blinkenjim/m404/eagle/m404.sch

## EAGLE design eagle/m404.sch (2017-06-18)

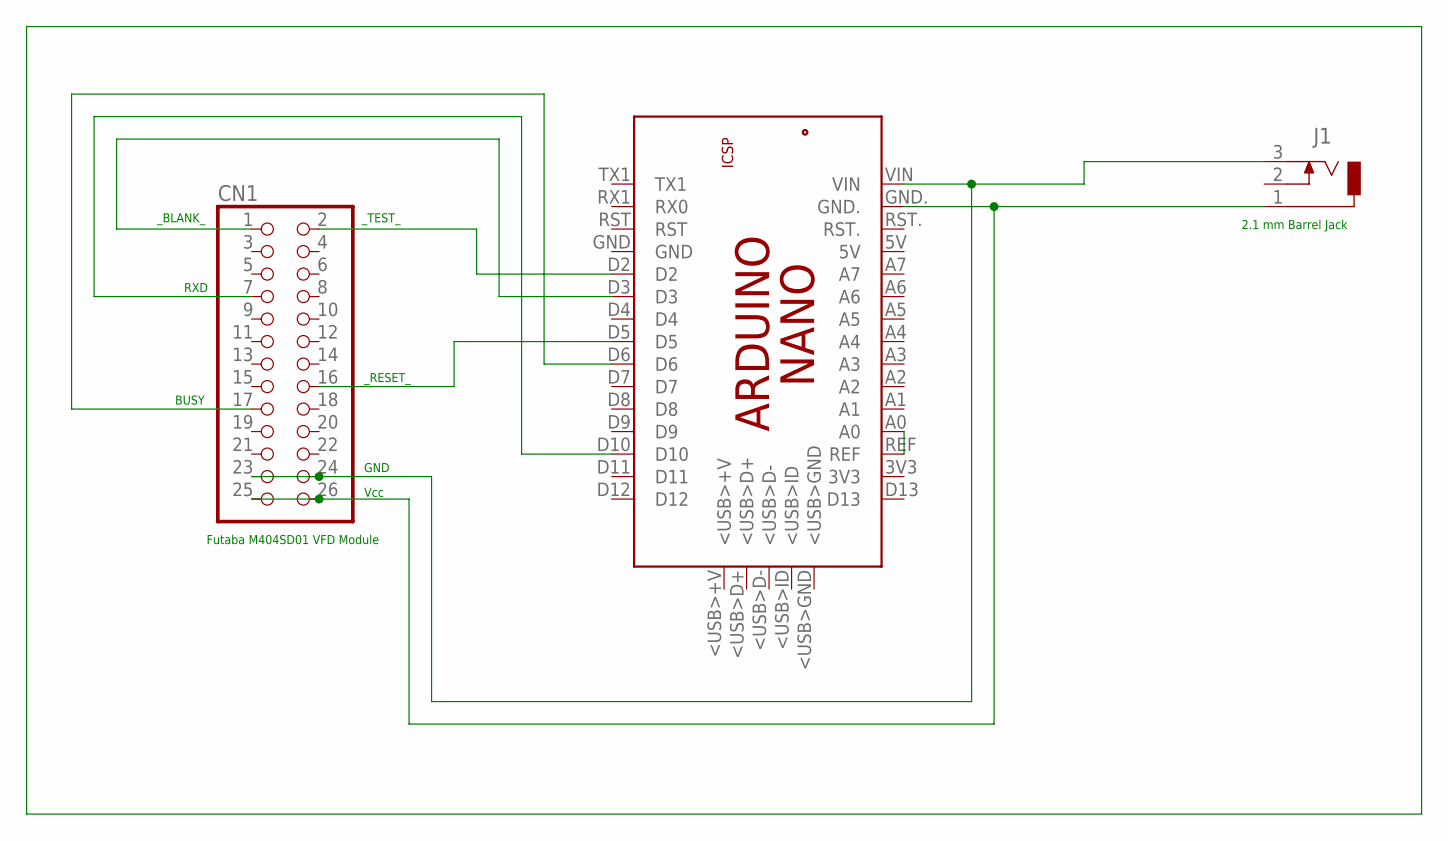
[picture p12: schematic m404.sch]

Parts:
CN1: PINHD-2X13; 2X13
J1: DCJ0202
PCB1: ARDUINO_NANO

Connections:
unnamed: CN1.25, CN1.26, J1.1, PCB1.GND.
unnamed: CN1.1, PCB1.D3
unnamed: CN1.23, CN1.24, J1.3, PCB1.VIN
unnamed: PCB1.A0, PCB1.REF
unnamed: CN1.2, PCB1.D2
unnamed: CN1.7, PCB1.D10
unnamed: CN1.16, PCB1.D5
unnamed: CN1.17, PCB1.D6

Notes on the sheet:
GND
Vcc
BUSY
RXD
_BLANK_
_TEST_
_RESET_
2.1 mm Barrel Jack
Futaba M404SD01 VFD Module
